the-butcher/MOTH.CO2.2/images/sensor03_800.jpg

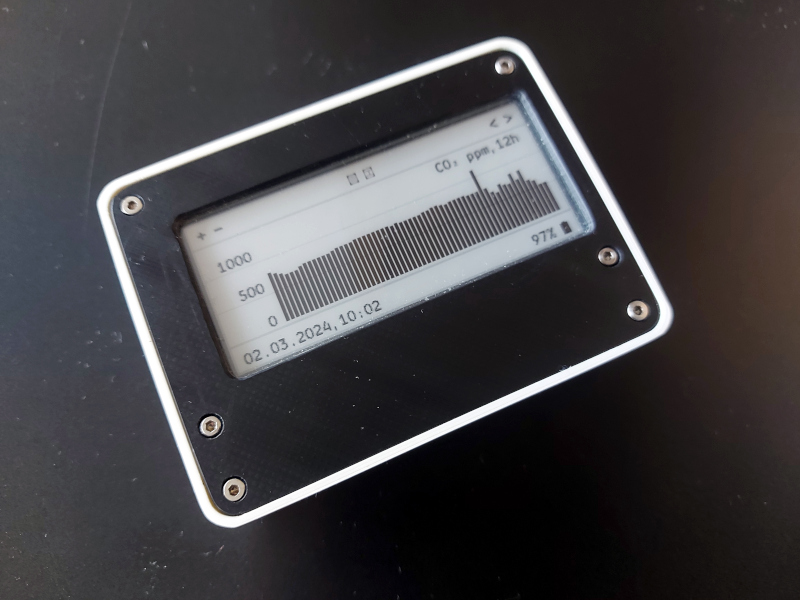
images/sensor03_800.jpg
