the-butcher/MOTH.CO2.2/images/sensor04_800.jpg

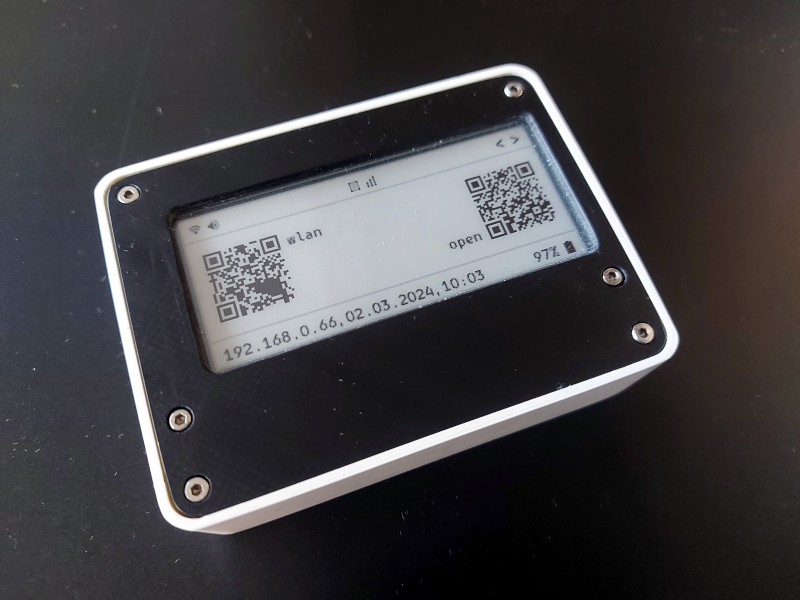
images/sensor04_800.jpg
