the-butcher/MOTH.CO2.2/moth_core/moth_core_022/src/sensors/SensorBme280.h

#ifndef SensorBme280_h
#define SensorBme280_h

#include <Adafruit_Sensor.h>
#include <Arduino.h>
#include <SPI.h>
#include <Wire.h>

#include "SensorBme280Base.h"
#include "types/Config.h"
#include "types/Values.h"

const float ALTITUDE__EXP = 0.190284;
const float ALTITUDE_MULT = 44307.69396;
const float PRESSURE_ZERO = 1013.25;

class SensorBme280 {
   private:
    static SensorBme280Base baseSensor;
    static values_bme_t values;

   public:
    static void begin();
    static bool measure();
    static values_bme_t readval();
    static float getPressureZerolevel(float altitudeBaselevel, float pressure);
    static float getAltitude(float pressureZerolevel, float pressure);
};

#endif
