the-butcher/MOTH.CO2.2/moth_core/moth_core_021/src/SensorScd041Base.h

#ifndef SensorScd041Base_h
#define SensorScd041Base_h

#include <SensirionI2CScd4x.h>

/**
 * subclass of SensirionI2CScd4x implementing a "no delay" version of
 * measureSingleShot
 */
class SensorScd041Base : public SensirionI2CScd4x {
   private:
    TwoWire* _i2cBus = nullptr;

   public:
    void begin(TwoWire& i2cBus);
    uint16_t measureSingleShotNoDelay(void);
};

#endif
