the-butcher/MOTH.CO2.2/moth_core/moth_core_022/src/modules/ModuleDisp.cpp

#include "ModuleDisp.h"

#include <ArduinoJson.h>
#include <qrcode.h>

#include "buttons/ButtonAction.h"
#include "modules/ModuleCard.h"
#include "sensors/SensorBme280.h"
#include "sensors/SensorEnergy.h"
#include "sensors/SensorScd041.h"
#include "sensors/SensorTime.h"
#include "types/Define.h"

const uint16_t LIMIT_POS_X = 287;
const uint8_t CHAR_DIM_X6 = 7;

const rectangle_t RECT_TOP = {1, 1, 295, 22};
const rectangle_t RECT_BOT = {1, 106, 295, 127};
const rectangle_t RECT_CO2 = {1, 22, 207, 106};
const rectangle_t RECT_DEG = {207, 22, 295, 64};
const rectangle_t RECT_HUM = {207, 64, 295, 106};
const rectangle_t RECT_NRG = {279, 112, 288, 125};
const int TEXT_OFFSET_Y = 16;

const char FORMAT_3_DIGIT[] = "%3s";
const char FORMAT_4_DIGIT[] = "%4s";
const char FORMAT_5_DIGIT[] = "%5s";
const char FORMAT_6_DIGIT[] = "%6s";
const char FORMAT_CELL_PERCENT[] = "%5s%%";
const char FORMAT_STALE[] = "%3s%% stale";

ModuleDispBase ModuleDisp::baseDisplay;
bool ModuleDisp::interrupted = false;

void ModuleDisp::configure(config_t& config) {

    ModuleCard::begin();

    File32 dispFileJson;
    bool dispSuccess = dispFileJson.open(DISP_CONFIG_JSON.c_str(), O_RDONLY);
    if (dispSuccess) {
        JsonDocument jsonDocument;
        DeserializationError error = deserializeJson(jsonDocument, dispFileJson);
        if (!error) {

            config.disp.configStatus = CONFIG_STAT__APPLIED;

            // display minutes
            config.disp.displayUpdateMinutes = jsonDocument[JSON_KEY___MINUTES] | config.disp.displayUpdateMinutes;  // apply network expiry (independant from networks)

            // show significant scale
            bool isShowSignificant = jsonDocument[JSON_KEY_______SSC] | config.disp.displayValCycle == DISPLAY_VAL_Y____SIG;
            config.disp.displayValCycle = isShowSignificant ? DISPLAY_VAL_Y____SIG : DISPLAY_VAL_Y____FIX;

            // display co2 threshold and reference
            config.disp.thresholdsCo2.wHi = jsonDocument[JSON_KEY_______CO2][JSON_KEY_WARN_HIGH] | config.disp.thresholdsCo2.wHi;
            config.disp.thresholdsCo2.rHi = jsonDocument[JSON_KEY_______CO2][JSON_KEY_RISK_HIGH] | config.disp.thresholdsCo2.rHi;
            config.disp.thresholdsCo2.ref = jsonDocument[JSON_KEY_______CO2][JSON_KEY_REFERENCE] | config.disp.thresholdsCo2.ref;

            // display deg thresholds
            config.disp.thresholdsDeg.rLo = jsonDocument[JSON_KEY_______DEG][JSON_KEY_RISK__LOW] | config.disp.thresholdsDeg.rLo;
            config.disp.thresholdsDeg.wLo = jsonDocument[JSON_KEY_______DEG][JSON_KEY_WARN__LOW] | config.disp.thresholdsDeg.wLo;
            config.disp.thresholdsDeg.wHi = jsonDocument[JSON_KEY_______DEG][JSON_KEY_WARN_HIGH] | config.disp.thresholdsDeg.wHi;
            config.disp.thresholdsDeg.rHi = jsonDocument[JSON_KEY_______DEG][JSON_KEY_RISK_HIGH] | config.disp.thresholdsDeg.rHi;

            // display deg scale (unit)
            bool isFahrenheit = jsonDocument[JSON_KEY_______DEG][JSON_KEY_______C2F] | config.disp.displayDegScale == DISPLAY_VAL_D______F;
            config.disp.displayDegScale = isFahrenheit ? DISPLAY_VAL_D______F : DISPLAY_VAL_D______C;

            // display deg offset
            config.sco2.temperatureOffset = jsonDocument[JSON_KEY_______DEG][JSON_KEY____OFFSET] | config.sco2.temperatureOffset;
            config.sco2.lpFilterRatioCurr = jsonDocument[JSON_KEY_______CO2][JSON_KEY_______LPA] | config.sco2.lpFilterRatioCurr;
            config.sco2.calibrationCo2Ref = jsonDocument[JSON_KEY_______CO2][JSON_KEY_______CAL] | config.sco2.calibrationCo2Ref;

            // display hum thresholds
            config.disp.thresholdsHum.rLo = jsonDocument[JSON_KEY_______HUM][JSON_KEY_RISK__LOW] | config.disp.thresholdsHum.rLo;
            config.disp.thresholdsHum.wLo = jsonDocument[JSON_KEY_______HUM][JSON_KEY_WARN__LOW] | config.disp.thresholdsHum.wLo;
            config.disp.thresholdsHum.wHi = jsonDocument[JSON_KEY_______HUM][JSON_KEY_WARN_HIGH] | config.disp.thresholdsHum.wHi;
            config.disp.thresholdsHum.rHi = jsonDocument[JSON_KEY_______HUM][JSON_KEY_RISK_HIGH] | config.disp.thresholdsHum.rHi;

            // altitude base level (home altitude of sensor)
            config.sbme.altitudeBaselevel = jsonDocument[JSON_KEY_______BME][JSON_KEY__ALTITUDE] | config.sbme.altitudeBaselevel;
            config.sbme.lpFilterRatioCurr = jsonDocument[JSON_KEY_______BME][JSON_KEY_______LPA] | config.sbme.lpFilterRatioCurr;

            String timezone = jsonDocument[JSON_KEY__TIMEZONE] | "";
            if (timezone != "") {
                timezone.toCharArray(config.time.timezone, 64);
            }

        } else {
            // TODO :: handle this condition
        }
        dispFileJson.close();
    }
}

void ModuleDisp::begin() {
    // do nothing
}

void ModuleDisp::prepareSleep(wakeup_action_e wakeupType) {
    if (wakeupType == WAKEUP_ACTION_BUSY) {
        esp_sleep_enable_ext0_wakeup((gpio_num_t)PIN_EPD_BUSY, HIGH);
    }
}

void ModuleDisp::attachWakeup(wakeup_action_e wakeupType) {
    if (wakeupType == WAKEUP_ACTION_BUSY) {
        attachInterrupt(digitalPinToInterrupt(PIN_EPD_BUSY), ModuleDisp::handleInterrupt, FALLING);
        ModuleDisp::interrupted = false;
    }
}

void ModuleDisp::detachWakeup(wakeup_action_e wakeupType) {
    if (wakeupType == WAKEUP_ACTION_BUSY) {
        detachInterrupt(digitalPinToInterrupt(PIN_EPD_BUSY));
        ModuleDisp::interrupted = false;
    }
}

void ModuleDisp::handleInterrupt() {
    ModuleDisp::interrupted = true;
}

bool ModuleDisp::isInterrupted() {
    return ModuleDisp::interrupted;
}

void ModuleDisp::flushBuffer() {
    ModuleDisp::baseDisplay.writeFrameBuffers();
}

void ModuleDisp::depower() {
    ModuleDisp::baseDisplay.begin(THINKINK_GRAYSCALE4, true);
    ModuleDisp::baseDisplay.depower();
}

void ModuleDisp::clearBuffer(config_t& config) {
    ModuleDisp::baseDisplay.begin(THINKINK_GRAYSCALE4, config.disp.displayValTheme == DISPLAY_THM____LIGHT);
    ModuleDisp::baseDisplay.clearBuffer();
}

void ModuleDisp::renderTable(values_all_t& measurement, config_t& config) {

    ModuleDisp::clearBuffer(config);
    ModuleDisp::drawOuterBorders(EPD_LIGHT);
    ModuleDisp::drawInnerBorders(EPD_LIGHT);

    // values for temperature and humidity
    float deg = SensorScd041::toFloatDeg(measurement.valuesCo2.deg);
    float hum = SensorScd041::toFloatHum(measurement.valuesCo2.hum);

    // variables needed
    String title;
    uint8_t textColor;
    uint8_t fillColor;
    uint8_t vertColor;
    uint16_t xPosMainValue = 36;
    uint16_t charPosValueX = 193;
    uint16_t charPosFinalX;

    if (config.disp.displayValTable == DISPLAY_VAL_T____CO2) {

        thresholds_co2_t thresholdsCo2 = config.disp.thresholdsCo2;
        float co2Lpf = measurement.valuesCo2.co2Lpf / VALUE_SCALE_CO2LPF;

        float stale = max(0.0f, min(10.0f, (co2Lpf - thresholdsCo2.ref) / 380.0f));  // don't allow negative stale values. max out at 10
        float staleWarn = max(0.0f, min(10.0f, (thresholdsCo2.wHi - thresholdsCo2.ref) / 380.0f));
        float staleRisk = max(0.0f, min(10.0f, (thresholdsCo2.rHi - thresholdsCo2.ref) / 380.0f));

        float staleMax = 2.5;
        if (stale > 4) {
            staleMax = 10;
        } else if (stale > 2) {
            staleMax = 5;
        }
        int staleDif = 70 / staleMax;  // height of 1 percent, 20 for staleMax 2.5, 10 for staleMax 5, 5 for staleMax 10

        textColor = getTextColor(co2Lpf, 0, 0, thresholdsCo2.wHi, thresholdsCo2.rHi);
        fillColor = getFillColor(co2Lpf, 0, 0, thresholdsCo2.wHi, thresholdsCo2.rHi);
        vertColor = getVertColor(co2Lpf, 0, 0, thresholdsCo2.wHi, thresholdsCo2.rHi);

        if (fillColor != EPD_WHITE) {
            ModuleDisp::fillRectangle(RECT_CO2, fillColor);
        }

        title = "CO² ppm";
        charPosFinalX = charPosValueX - CHAR_DIM_X6 * 7;
        ModuleDisp::drawAntialiasedText36(formatString(String(co2Lpf, 0), FORMAT_4_DIGIT), RECT_CO2, xPosMainValue, 76, textColor);

        uint8_t yMax = RECT_CO2.ymax - 7;  // bottom limit of rebreathe indicator
        uint8_t yDim = round(stale * staleDif);
        uint8_t yDimWarn = round(staleWarn * staleDif);
        uint8_t yDimRisk = round(staleRisk * staleDif);
        int yDimMax = round(staleMax * staleDif);

        uint8_t xBarMin = 8;
        uint8_t xBarMax = 13;
        for (uint8_t i = xBarMin; i <= xBarMax; i++) {
            ModuleDisp::baseDisplay.drawFastVLine(i, yMax - yDimWarn, yDimWarn, EPD_WHITE);             // good
            ModuleDisp::baseDisplay.drawFastVLine(i, yMax - yDimRisk, yDimRisk - yDimWarn, vertColor);  // warn
            ModuleDisp::baseDisplay.drawFastVLine(i, yMax - yDimMax, yDimMax - yDimRisk, EPD_BLACK);    // risk
        }

        if (ModuleDisp::isRisk(co2Lpf, 0, 0, thresholdsCo2.wHi, thresholdsCo2.rHi)) {  // when in risk, the risk area needs to be outlined
            ModuleDisp::baseDisplay.drawFastVLine(xBarMin, yMax - yDimMax, yDimMax - yDimRisk, vertColor);
            ModuleDisp::baseDisplay.drawFastVLine(xBarMax, yMax - yDimMax, yDimMax - yDimRisk, vertColor);
            ModuleDisp::baseDisplay.drawFastHLine(xBarMin, yMax - yDimMax, xBarMax - xBarMin + 1, vertColor);
        } else if (!ModuleDisp::isWarn(co2Lpf, 0, 0, thresholdsCo2.wHi, thresholdsCo2.rHi)) {  // when not warn and not risk, the good area needs to be outlined
            ModuleDisp::baseDisplay.drawFastVLine(xBarMin, yMax - yDimWarn, yDimWarn, vertColor);
            ModuleDisp::baseDisplay.drawFastVLine(xBarMax, yMax - yDimWarn, yDimWarn, vertColor);
            ModuleDisp::baseDisplay.drawFastHLine(xBarMin, yMax, xBarMax - xBarMin + 1, vertColor);
        }

        uint8_t yTxt = RECT_CO2.ymax - RECT_CO2.ymin - yDim - 10;
        uint8_t yPrc = yTxt;
        uint8_t xPrc = xBarMax + 19;
        uint8_t xLin = 24;

        uint8_t stale10 = round(stale * 10.0);
        uint8_t staleFix = floor(stale10 / 10.0);
        uint8_t staleFrc = abs(stale10 % 10);

        if (stale > 8.5) {
            yTxt += 14;
            yPrc += 14;
        } else if (co2Lpf >= 1000) {  // wrap percent, shorten line
            yPrc += 14;
            xPrc = xBarMax + 2;
            xLin -= CHAR_DIM_X6;
        }

        // draw a narrowed percentage number
        ModuleDisp::baseDisplay.drawFastHLine(xBarMax + 3, yMax - yDim, xLin, textColor);
        ModuleDisp::drawAntialiasedText06(String(staleFix), RECT_CO2, xBarMax + 2, yTxt, textColor);
        if (stale < 10) {
            ModuleDisp::drawAntialiasedText06(".", RECT_CO2, xBarMax + 7, yTxt, textColor);
            ModuleDisp::drawAntialiasedText06(String(staleFrc), RECT_CO2, xBarMax + 12, yTxt, textColor);
        }
        ModuleDisp::drawAntialiasedText06("%", RECT_CO2, xPrc, yPrc, textColor);

    } else if (config.disp.displayValTable == DISPLAY_VAL_T____HPA) {
        float pressure = measurement.valuesBme.pressure;
        textColor = EPD_BLACK;
        fillColor = EPD_WHITE;
        vertColor = EPD_DARK;
        ModuleDisp::fillRectangle(RECT_CO2, fillColor);
        title = "pressure hPa";
        charPosFinalX = charPosValueX - CHAR_DIM_X6 * title.length();
        ModuleDisp::drawAntialiasedText36(formatString(String(pressure, 0), FORMAT_4_DIGIT), RECT_CO2, xPosMainValue, 76, textColor);
    } else if (config.disp.displayValTable == DISPLAY_VAL_T____ALT) {
        float altitude = SensorBme280::getAltitude(config.sbme.pressureZerolevel, measurement.valuesBme.pressure);
        textColor = EPD_BLACK;
        fillColor = EPD_WHITE;
        vertColor = EPD_DARK;
        ModuleDisp::fillRectangle(RECT_CO2, fillColor);
        title = "altitude m";
        charPosFinalX = charPosValueX - CHAR_DIM_X6 * title.length();
        ModuleDisp::drawAntialiasedText36(formatString(String(altitude, 0), FORMAT_4_DIGIT), RECT_CO2, xPosMainValue, 76, textColor);
    } else {
        // TODO :: handle this (unknown display value)
    }
    ModuleDisp::drawAntialiasedText06(title, RECT_CO2, charPosFinalX, TEXT_OFFSET_Y, textColor);

    thresholds_deg_t thresholdsDeg = config.disp.thresholdsDeg;
    textColor = getTextColor(deg, thresholdsDeg.rLo, thresholdsDeg.wLo, thresholdsDeg.wHi, thresholdsDeg.rHi);
    fillColor = getFillColor(deg, thresholdsDeg.rLo, thresholdsDeg.wLo, thresholdsDeg.wHi, thresholdsDeg.rHi);
    if (config.disp.displayDegScale == DISPLAY_VAL_D______F) {
        deg = SensorScd041::toFahrenheit(deg);
    }
    int temperature10 = round(deg * 10.0);
    int temperatureFix = floor(temperature10 / 10.0);
    int temperatureFrc = abs(temperature10 % 10);
    if (fillColor != EPD_WHITE) {
        ModuleDisp::fillRectangle(RECT_DEG, fillColor);
    }
    ModuleDisp::drawAntialiasedText18(formatString(String(temperatureFix), FORMAT_3_DIGIT), RECT_DEG, 0, 35, textColor);
    ModuleDisp::drawAntialiasedText06(config.disp.displayDegScale == DISPLAY_VAL_D______F ? "°F" : "°C", RECT_DEG, 80 - CHAR_DIM_X6 * 2, TEXT_OFFSET_Y + 2, textColor);
    ModuleDisp::drawAntialiasedText08(".", RECT_DEG, 63, 35, textColor);
    ModuleDisp::drawAntialiasedText08(String(temperatureFrc), RECT_DEG, 72, 35, textColor);

    // TODO :: remove after the reason for wifi can not be turned was found and the problem was fixed
    // ModuleDisp::drawAntialiasedText06(String(config.wifi.wifiValPower), RECT_DEG, 7, TEXT_OFFSET_Y + 2, textColor);

    thresholds_hum_t thresholdsHum = config.disp.thresholdsHum;
    textColor = getTextColor(hum, thresholdsHum.rLo, thresholdsHum.wLo, thresholdsHum.wHi, thresholdsHum.rHi);
    fillColor = getFillColor(hum, thresholdsHum.rLo, thresholdsHum.wLo, thresholdsHum.wHi, thresholdsHum.rHi);
    int humidity10 = round(hum * 10.0);
    int humidityFix = floor(humidity10 / 10.0);
    int humidityFrc = abs(humidity10 % 10);
    if (fillColor != EPD_WHITE) {
        ModuleDisp::fillRectangle(RECT_HUM, fillColor);
    }
    ModuleDisp::drawAntialiasedText18(formatString(String(humidityFix), FORMAT_3_DIGIT), RECT_HUM, 0, 35, textColor);
    ModuleDisp::drawAntialiasedText06("%", RECT_HUM, 80 - CHAR_DIM_X6 * 1, TEXT_OFFSET_Y + 2, textColor);
    ModuleDisp::drawAntialiasedText08(".", RECT_HUM, 63, 35, textColor);
    ModuleDisp::drawAntialiasedText08(String(humidityFrc), RECT_HUM, 72, 35, textColor);

    ModuleDisp::renderHeader();
    ModuleDisp::renderFooter(config);

    ModuleDisp::flushBuffer();
}

/**
 * measurement is reference for building the measurement table backwards
 */
void ModuleDisp::renderChart(values_all_t history[60], config_t& config) {

    ModuleDisp::clearBuffer(config);
    ModuleDisp::drawOuterBorders(EPD_LIGHT);

    display_val_c_e displayValChart = config.disp.displayValChart;

    values_all_t measurement;
    uint16_t minValue = 0;
    uint16_t maxValue = 1500;
    if (displayValChart == DISPLAY_VAL_C____CO2) {
        float co2Lpf;
        for (uint8_t i = 0; i < HISTORY_____BUFFER_SIZE; i++) {
            measurement = history[i];
            co2Lpf = measurement.valuesCo2.co2Lpf / VALUE_SCALE_CO2LPF;
            if (co2Lpf > 3600) {
                maxValue = 6000;  // 0, 2000, 4000, (6000)
            } else if (co2Lpf > 2400) {
                maxValue = 4500;  // 0, 1500, 3000, (4500)
            } else if (co2Lpf > 1200) {
                maxValue = 3000;  // 0, 1000, 2000, (3000)
            }
        }
    } else if (displayValChart == DISPLAY_VAL_C____DEG) {
        if (config.disp.displayDegScale == DISPLAY_VAL_D______F) {
            minValue = 60;
            maxValue = 120;
        } else {
            minValue = 10;
            maxValue = 40;
        }
    } else if (displayValChart == DISPLAY_VAL_C____HUM) {
        minValue = 20;
        maxValue = 80;  // 20, 40, 60, (80)
    } else if (displayValChart == DISPLAY_VAL_C____HPA) {
        double pressureAvg = 0;
        uint8_t validValueCount = 0;
        for (uint8_t i = 0; i < HISTORY_____BUFFER_SIZE; i++) {
            measurement = history[i];
            if (measurement.valuesBme.pressure > 0) {
                pressureAvg += measurement.valuesBme.pressure;
                validValueCount++;
            }
        }
        pressureAvg /= validValueCount;                  // lets say it is 998
        minValue = floor(pressureAvg / 10.0) * 10 - 10;  // 99.8 -> 99 -> 990 -> 980
        maxValue = ceil(pressureAvg / 10.0) * 10 + 10;   // 99.8 -> 100 -> 1000 -> 1010
    } else if (displayValChart == DISPLAY_VAL_C____ALT) {
        maxValue = 450;
        float altitude;
        for (uint8_t i = 0; i < HISTORY_____BUFFER_SIZE; i++) {
            measurement = history[i];
            if (measurement.valuesBme.pressure > 0) {
                altitude = SensorBme280::getAltitude(config.sbme.pressureZerolevel, measurement.valuesBme.pressure);
            } else {
                altitude = 0.0f;
            }
            if (altitude > 1600) {
                maxValue = 3600;  // 0, 1200, 2400, 3600
            } else if (altitude > 800) {
                maxValue = 1800;  // 0, 600, 1200, (1800)
            } else if (altitude > 400) {
                maxValue = 900;  // 0, 300, 600, (900)
            }
        }
    } else if (displayValChart == DISPLAY_VAL_C____NRG) {
        double batteryAvg = 0;
        float batteryVal;
        float batteryMin = 100;
        float batteryMax = 0;
        uint8_t validValueCount = 0;
        for (uint8_t i = 0; i < HISTORY_____BUFFER_SIZE; i++) {
            measurement = history[i];
            if (measurement.valuesBme.pressure > 0) {  // is it a valid value?
                batteryVal = SensorEnergy::toFloatPercent(measurement.valuesNrg.percent);
                batteryMin = min(batteryMin, batteryVal);
                batteryMax = max(batteryMax, batteryVal);
                batteryAvg += batteryVal;
                validValueCount++;
            }
        }
        batteryAvg /= validValueCount;
        batteryAvg = round(batteryAvg);

        double batteryDif = max(2.0, ceil((batteryMax - batteryMin) / 2.0));  // half dif from min to max, min 1
        if (batteryAvg > 50) {
            maxValue = min(100.0, batteryAvg + batteryDif);  // avg + dif (but not more than 100)
            minValue = maxValue - batteryDif * 2;
        } else {
            minValue = max(0.0, batteryAvg - batteryDif);  // avg - dif (but not less than zero)
            maxValue = minValue + batteryDif * 2;
        }
        maxValue += batteryDif;  // room for text
    }

    String label2 = String(minValue + (maxValue - minValue) * 2 / 3);
    String label1 = String(minValue + (maxValue - minValue) / 3);
    String label0 = String(minValue);

    uint8_t charPosValueX = 41;
    uint8_t charPosLabelY = 12;

    ModuleDisp::drawAntialiasedText06(label2, RECT_CO2, charPosValueX - CHAR_DIM_X6 * label2.length(), 24, EPD_BLACK);
    ModuleDisp::baseDisplay.drawFastHLine(1, 49, 296, EPD_LIGHT);
    ModuleDisp::drawAntialiasedText06(label1, RECT_CO2, charPosValueX - CHAR_DIM_X6 * label1.length(), 52, EPD_BLACK);
    ModuleDisp::baseDisplay.drawFastHLine(1, 77, 296, EPD_LIGHT);
    ModuleDisp::drawAntialiasedText06(label0, RECT_CO2, charPosValueX - CHAR_DIM_X6 * label0.length(), 80, EPD_BLACK);

    values_all_t lastMeasurement = history[HISTORY_____BUFFER_SIZE - 1];
    String label;
    String value;
    String vunit;
    if (displayValChart == DISPLAY_VAL_C____CO2) {
        label = "CO²";
        value = String(lastMeasurement.valuesCo2.co2Lpf / VALUE_SCALE_CO2LPF, 0);
        vunit = "ppm";
    } else if (displayValChart == DISPLAY_VAL_C____DEG) {
        label = "temperature";
        value = String(SensorScd041::toFloatDeg(lastMeasurement.valuesCo2.deg), 1);
        vunit = config.disp.displayDegScale == DISPLAY_VAL_D______F ? "°F" : "°C";
    } else if (displayValChart == DISPLAY_VAL_C____HUM) {
        label = "humidity";
        value = String(SensorScd041::toFloatHum(lastMeasurement.valuesCo2.hum), 1);
        vunit = "%";
    } else if (displayValChart == DISPLAY_VAL_C____HPA) {
        label = "pressure";
        value = String(lastMeasurement.valuesBme.pressure, 0);
        vunit = "hPa";
    } else if (displayValChart == DISPLAY_VAL_C____ALT) {
        label = "altitude";
        if (measurement.valuesBme.pressure > 0) {
            value = String(SensorBme280::getAltitude(config.sbme.pressureZerolevel, lastMeasurement.valuesBme.pressure), 0);
        } else {
            value = String(0.0f, 0);
        }
        vunit = "m";  // TODO :: allow feet (?)
    } else if (displayValChart == DISPLAY_VAL_C____NRG) {
        label = "battery";
        value = String(SensorEnergy::toFloatPercent(lastMeasurement.valuesNrg.percent), 0);
        vunit = "%";
    }

    char titleBuffer[32];
    sprintf(titleBuffer, "%s (%s%s),%dh", label, value, vunit, config.disp.displayHrsChart);
    String title = String(titleBuffer);

    ModuleDisp::drawAntialiasedText06(title, RECT_CO2, LIMIT_POS_X - title.length() * CHAR_DIM_X6 + 1, charPosLabelY, EPD_BLACK);

    uint16_t minX;
    uint8_t minY;
    uint8_t maxY = 103;
    uint8_t dimY;
    uint8_t limY = 78.0;
    float curValue;

    uint8_t displayableBarWidth = 240 / HISTORY_____BUFFER_SIZE;
    uint8_t basX = LIMIT_POS_X - HISTORY_____BUFFER_SIZE * displayableBarWidth;
    for (uint8_t i = 0; i < HISTORY_____BUFFER_SIZE; i++) {

        measurement = history[i];

        if (displayValChart == DISPLAY_VAL_C____CO2) {
            curValue = measurement.valuesCo2.co2Lpf / VALUE_SCALE_CO2LPF;
        } else if (displayValChart == DISPLAY_VAL_C____DEG) {
            curValue = SensorScd041::toFloatDeg(measurement.valuesCo2.deg);
            if (config.disp.displayDegScale == DISPLAY_VAL_D______F) {
                curValue = SensorScd041::toFahrenheit(curValue);
            }
        } else if (displayValChart == DISPLAY_VAL_C____HUM) {
            curValue = SensorScd041::toFloatHum(measurement.valuesCo2.hum);
        } else if (displayValChart == DISPLAY_VAL_C____HPA) {
            curValue = measurement.valuesBme.pressure;
        } else if (displayValChart == DISPLAY_VAL_C____ALT) {
            if (measurement.valuesBme.pressure > 0) {
                curValue = SensorBme280::getAltitude(config.sbme.pressureZerolevel, measurement.valuesBme.pressure);
            } else {
                curValue = 0.0f;
            }
        } else if (displayValChart == DISPLAY_VAL_C____NRG) {
            curValue = SensorEnergy::toFloatPercent(measurement.valuesNrg.percent);
        }

        minX = basX + i * displayableBarWidth;
        dimY = max(0, min((int)limY, (int)round((curValue - minValue) * limY / (maxValue - minValue))));
        minY = maxY - dimY;

        if (dimY > 0) {
            for (int b = 0; b < displayableBarWidth - 1; b++) {
                baseDisplay.drawFastVLine(minX + b, minY, dimY, EPD_BLACK);
            }
        } else {
            // indicator lines
            // baseDisplay.drawFastHLine(minX, minY - 1, displayableBarWidth - 1, EPD_BLACK);
        }
    }

    ModuleDisp::renderHeader();
    ModuleDisp::renderFooter(config);

    ModuleDisp::flushBuffer();
}

void ModuleDisp::renderCo2Cal(co2cal______t co2cal, config_t& config) {

    ModuleDisp::clearBuffer(config);
    ModuleDisp::drawOuterBorders(EPD_LIGHT);

    values_all_t measurement;
    uint16_t minValue = co2cal.minValue - 50;
    uint16_t maxValue = co2cal.maxValue + 50;

    uint16_t minX;
    uint8_t minY;
    uint8_t maxY = 103;
    uint8_t dimY;
    uint8_t limY = 78;
    float curValue;

    curValue = co2cal.avgValue - co2cal.devValue;
    dimY = max(0, min((int)limY, (int)round((curValue - minValue) * limY / (maxValue - minValue))));
    uint8_t maxD = max((uint8_t)22, min((uint8_t)105, (uint8_t)(maxY - dimY)));
    curValue = co2cal.avgValue + co2cal.devValue;
    dimY = max(0, min((int)limY, (int)round((curValue - minValue) * limY / (maxValue - minValue))));
    uint8_t minD = max((uint8_t)22, min((uint8_t)105, (uint8_t)(maxY - dimY)));

    for (uint8_t devD = minD; devD <= maxD; devD++) {
        baseDisplay.drawFastHLine(5, devD, 286, EPD_LIGHT);
    }

    uint8_t displayableBarWidth = 220 / CALIBRATION_BUFFER_SIZE;
    uint8_t basX = LIMIT_POS_X - CALIBRATION_BUFFER_SIZE * displayableBarWidth;
    for (uint8_t i = 0; i < CALIBRATION_BUFFER_SIZE; i++) {

        curValue = co2cal.values[i];

        minX = basX + i * displayableBarWidth;
        dimY = max(0, min((int)limY, (int)round((curValue - minValue) * limY / (maxValue - minValue))));
        minY = maxY - dimY;

        if (dimY > 0) {
            for (int b = 0; b < displayableBarWidth - 1; b++) {
                baseDisplay.drawFastVLine(minX + b, minY, dimY, EPD_DARK);  // draw line top down
            }
        } else {
            // indicator lines
            // baseDisplay.drawFastHLine(minX, minY - 1, displayableBarWidth - 1, EPD_BLACK);
        }
    }

    // avg indicator line
    curValue = co2cal.avgValue;
    dimY = max(0, min((int)limY, (int)round((curValue - minValue) * limY / (maxValue - minValue))));
    minY = maxY - dimY;
    baseDisplay.drawFastHLine(5, minY, 286, EPD_BLACK);

    String labelAvg = String(curValue, 0);
    String labelDev = String(co2cal.devValue);
    String labelTop = String(co2cal.maxValue);
    String labelBot = String(co2cal.minValue);
    if (co2cal.type == CO2CAL_SUCCESS) {
        labelTop = "success";
        labelBot = String(co2cal.corValue);
    } else if (co2cal.type == CO2CAL_FAILURE) {
        labelTop = "failure";
        labelBot = "";
    }

    uint8_t charPosValueX = 61;
    uint8_t charPosValueY = minY - 4;
    ModuleDisp::drawAntialiasedText06(labelAvg, RECT_TOP, charPosValueX - CHAR_DIM_X6 * labelAvg.length(), charPosValueY, EPD_BLACK);       // use RECT_TOP becuase it refers to Y=0
    ModuleDisp::drawAntialiasedText06(labelDev, RECT_TOP, charPosValueX - CHAR_DIM_X6 * labelDev.length(), charPosValueY + 14, EPD_BLACK);  // use RECT_TOP becuase it refers to Y=0
    ModuleDisp::drawAntialiasedText06(labelTop, RECT_CO2, charPosValueX - CHAR_DIM_X6 * labelTop.length(), 12, EPD_BLACK);
    ModuleDisp::drawAntialiasedText06(labelBot, RECT_CO2, charPosValueX - CHAR_DIM_X6 * labelBot.length(), 80, EPD_BLACK);

    ModuleDisp::renderHeader();
    ModuleDisp::renderFooter(config);

    ModuleDisp::flushBuffer();
}

void ModuleDisp::renderHeader() {
    renderButton(ButtonAction::A.buttonAction, 6);
    renderButton(ButtonAction::B.buttonAction, 135);
    renderButton(ButtonAction::C.buttonAction, 264);
}

void ModuleDisp::renderButton(button_action_t buttonAction, uint16_t x) {
    ModuleDisp::drawAntialiasedText08(buttonAction.symbolSlow, RECT_TOP, x, TEXT_OFFSET_Y, EPD_BLACK);
    ModuleDisp::drawAntialiasedText08(buttonAction.symbolFast, RECT_TOP, x + CHAR_DIM_X6 * 2, TEXT_OFFSET_Y, EPD_BLACK);
    ModuleDisp::drawAntialiasedText06(buttonAction.extraLabel, RECT_TOP, x + CHAR_DIM_X6 * 4, TEXT_OFFSET_Y - 2, EPD_BLACK);
}

void ModuleDisp::renderFooter(config_t& config) {

    values_nrg_t valuesEnergy = SensorEnergy::readval();
    float percent = SensorEnergy::toFloatPercent(valuesEnergy.percent);

    String cellPercentFormatted = formatString(String(percent, 0), FORMAT_CELL_PERCENT);
    ModuleDisp::drawAntialiasedText06(cellPercentFormatted, RECT_BOT, LIMIT_POS_X - 14 - CHAR_DIM_X6 * cellPercentFormatted.length(), TEXT_OFFSET_Y, EPD_BLACK);

    // main battery frame
    ModuleDisp::fillRectangle(RECT_NRG, EPD_LIGHT);

    // percentage
    uint8_t yMin = RECT_NRG.ymax - 3 - (uint8_t)round((RECT_NRG.ymax - RECT_NRG.ymin - 3) * percent * 0.01f);
    fillRectangle({RECT_NRG.xmin, yMin, RECT_NRG.xmax, RECT_NRG.ymax}, EPD_BLACK);

    // battery contact clip
    ModuleDisp::baseDisplay.drawFastHLine(RECT_NRG.xmin + 1, RECT_NRG.ymin + 1, 2, EPD_WHITE);
    ModuleDisp::baseDisplay.drawFastHLine(RECT_NRG.xmax - 3, RECT_NRG.ymin + 1, 2, EPD_WHITE);

    int charPosFooter = 7;
    if (config.sign.signalValSound == SIGNAL__VAL______ON) {
        ModuleDisp::drawAntialiasedText08(SYMBOL_YBEEP, RECT_BOT, 6, TEXT_OFFSET_Y + 1, EPD_BLACK);
        charPosFooter += 13;
    }

    if (config.wifi.wifiValPower == WIFI____VAL_P__CUR_Y) {
        String address = ModuleWifi::getAddress();
        ModuleDisp::drawAntialiasedText06(address, RECT_BOT, charPosFooter, TEXT_OFFSET_Y, EPD_BLACK);
        ModuleDisp::drawAntialiasedText06(",", RECT_BOT, charPosFooter + address.length() * CHAR_DIM_X6, TEXT_OFFSET_Y, EPD_BLACK);
        charPosFooter += (address.length() + 1) * CHAR_DIM_X6;
    }
    ModuleDisp::drawAntialiasedText06(SensorTime::getDateTimeDisplayString(SensorTime::getSecondstime()), RECT_BOT, charPosFooter, TEXT_OFFSET_Y, EPD_BLACK);
}

void ModuleDisp::renderEntry(config_t& config) {
    ModuleDisp::clearBuffer(config);
    ModuleDisp::drawOuterBorders(EPD_LIGHT);

    drawAntialiasedText18("moth", RECT_TOP, 8, 98, EPD_BLACK);
    drawAntialiasedText06(VNUM, RECT_TOP, 105, 98, EPD_BLACK);
    drawAntialiasedText06(String(Config::getUtcOffsetSeconds()), RECT_TOP, 180, 98, EPD_BLACK);

    // skip header for clean screen
    ModuleDisp::renderFooter(config);

    ModuleDisp::flushBuffer();
}

void ModuleDisp::renderQRCodes(config_t& config) {
    ModuleDisp::clearBuffer(config);
    ModuleDisp::drawOuterBorders(EPD_LIGHT);

    // either http://ap_ip/login or [PREF_A_WIFI] + IP
    String address = ModuleWifi::getRootUrl();
    String networkName = ModuleWifi::getNetworkName();
    String networkPass = ModuleWifi::getNetworkPass();

    int qrCodeX = 12;
    int qrCodeY = 35;

    // render the network connection link
    if (networkName != "") {
        char networkBuf[networkName.length() + 1];
        networkName.toCharArray(networkBuf, networkName.length() + 1);

        QRCode qrcodeNetwork;
        uint8_t qrcodeDataNetwork[qrcode_getBufferSize(3)];
        qrcode_initText(&qrcodeNetwork, qrcodeDataNetwork, 3, 0, networkBuf);

        for (uint8_t y = 0; y < qrcodeNetwork.size; y++) {
            for (uint8_t x = 0; x < qrcodeNetwork.size; x++) {
                if (qrcode_getModule(&qrcodeNetwork, x, y)) {
                    baseDisplay.fillRect(x * 2 + qrCodeX, y * 2 + qrCodeY, 2, 2, EPD_BLACK);
                }
            }
        }

        qrCodeX = 228;

        ModuleDisp::drawAntialiasedText06("wlan", RECT_TOP, 75, 45, EPD_BLACK);
        if (networkPass != "") {
            ModuleDisp::drawAntialiasedText06(ModuleWifi::getNetworkPass(), RECT_TOP, 75, 60, EPD_BLACK);
        }
        ModuleDisp::drawAntialiasedText06("open", RECT_TOP, 193, 89, EPD_BLACK);
    }

    char addressBuf[address.length() + 1];
    address.toCharArray(addressBuf, address.length() + 1);

    QRCode qrcodeAddress;
    uint8_t qrcodeDataAddress[qrcode_getBufferSize(3)];
    qrcode_initText(&qrcodeAddress, qrcodeDataAddress, 3, 0, addressBuf);

    // render the ip address within the network
    for (uint8_t y = 0; y < qrcodeAddress.size; y++) {
        for (uint8_t x = 0; x < qrcodeAddress.size; x++) {
            if (qrcode_getModule(&qrcodeAddress, x, y)) {
                baseDisplay.fillRect(x * 2 + qrCodeX, y * 2 + qrCodeY, 2, 2, EPD_BLACK);
            }
        }
    }

    ModuleDisp::renderHeader();
    ModuleDisp::renderFooter(config);

    ModuleDisp::flushBuffer();
}

void ModuleDisp::drawAntialiasedText06(String text, rectangle_t rectangle, int xRel, int yRel, uint8_t color) {
    drawAntialiasedText(text, rectangle, xRel, yRel, color, &smb06pt_l, &smb06pt_d, &smb06pt_b);
}

void ModuleDisp::drawAntialiasedText08(String text, rectangle_t rectangle, int xRel, int yRel, uint8_t color) {
    drawAntialiasedText(text, rectangle, xRel, yRel, color, &smb08pt_l, &smb08pt_d, &smb08pt_b);
}

void ModuleDisp::drawAntialiasedText18(String text, rectangle_t rectangle, int xRel, int yRel, uint8_t color) {
    drawAntialiasedText(text, rectangle, xRel, yRel, color, &smb18pt_l, &smb18pt_d, &smb18pt_b);
}

void ModuleDisp::drawAntialiasedText36(String text, rectangle_t rectangle, int xRel, int yRel, uint8_t color) {
    drawAntialiasedText(text, rectangle, xRel, yRel, color, &smb36pt_l, &smb36pt_d, &smb36pt_b);
}

/**
 * when switching fonts, setFont(...) must be called before setCursor(...), or there may be a y-offset on the very first text
 */
void ModuleDisp::drawAntialiasedText(String text, rectangle_t rectangle, int xRel, int yRel, uint8_t color, const GFXfont* fontL, const GFXfont* fontD, const GFXfont* fontB) {
    ModuleDisp::baseDisplay.setFont(fontL);
    ModuleDisp::baseDisplay.setCursor(rectangle.xmin + xRel, rectangle.ymin + yRel);
    ModuleDisp::baseDisplay.setTextColor(color == EPD_BLACK ? EPD_LIGHT : EPD_DARK);
    ModuleDisp::baseDisplay.print(text);

    ModuleDisp::baseDisplay.setFont(fontD);
    ModuleDisp::baseDisplay.setCursor(rectangle.xmin + xRel, rectangle.ymin + yRel);
    ModuleDisp::baseDisplay.setTextColor(color == EPD_BLACK ? EPD_DARK : EPD_LIGHT);
    ModuleDisp::baseDisplay.print(text);

    ModuleDisp::baseDisplay.setFont(fontB);
    ModuleDisp::baseDisplay.setCursor(rectangle.xmin + xRel, rectangle.ymin + yRel);
    ModuleDisp::baseDisplay.setTextColor(color);
    ModuleDisp::baseDisplay.print(text);
}

void ModuleDisp::drawOuterBorders(uint16_t color) {
    // top
    ModuleDisp::baseDisplay.drawFastHLine(0, 0, 296, color);
    ModuleDisp::baseDisplay.drawFastHLine(0, 1, 296, color);
    // footer separator
    ModuleDisp::baseDisplay.drawFastHLine(0, 105, 296, color);
    ModuleDisp::baseDisplay.drawFastHLine(0, 106, 296, color);
    // header separator
    ModuleDisp::baseDisplay.drawFastHLine(0, 21, 296, color);
    ModuleDisp::baseDisplay.drawFastHLine(0, 22, 296, color);
    // bottom
    ModuleDisp::baseDisplay.drawFastHLine(0, 126, 296, color);
    ModuleDisp::baseDisplay.drawFastHLine(0, 127, 296, color);
    // left
    ModuleDisp::baseDisplay.drawFastVLine(0, 0, 128, color);
    ModuleDisp::baseDisplay.drawFastVLine(1, 0, 128, color);
    // right
    ModuleDisp::baseDisplay.drawFastVLine(294, 0, 128, color);
    ModuleDisp::baseDisplay.drawFastVLine(295, 0, 128, color);
}

void ModuleDisp::drawInnerBorders(uint16_t color) {
    // horizontal center
    ModuleDisp::baseDisplay.drawFastHLine(206, 63, 100, color);
    ModuleDisp::baseDisplay.drawFastHLine(206, 64, 100, color);
    // vertical center
    ModuleDisp::baseDisplay.drawFastVLine(206, 21, 86, color);
    ModuleDisp::baseDisplay.drawFastVLine(207, 22, 86, color);
}

void ModuleDisp::fillRectangle(rectangle_t rectangle, uint8_t color) {
    ModuleDisp::baseDisplay.fillRect(rectangle.xmin + 1, rectangle.ymin + 1, rectangle.xmax - rectangle.xmin - 2, rectangle.ymax - rectangle.ymin - 2, color);
}

bool ModuleDisp::isWarn(float value, uint16_t rLo, uint16_t warnLo, uint16_t wHi, uint16_t rHi) {
    return value < warnLo || value >= wHi;
}

bool ModuleDisp::isRisk(float value, uint16_t rLo, uint16_t warnLo, uint16_t wHi, uint16_t rHi) {
    return value < rLo || value >= rHi;
}

uint8_t ModuleDisp::getTextColor(float value, uint16_t rLo, uint16_t warnLo, uint16_t wHi, uint16_t rHi) {
    if (ModuleDisp::isRisk(value, rLo, warnLo, wHi, rHi)) {
        return EPD_WHITE;
    } else {
        return EPD_BLACK;
    }
}

uint8_t ModuleDisp::getFillColor(float value, uint16_t rLo, uint16_t warnLo, uint16_t wHi, uint16_t rHi) {
    if (ModuleDisp::isRisk(value, rLo, warnLo, wHi, rHi)) {
        return EPD_BLACK;
    } else if (ModuleDisp::isWarn(value, rLo, warnLo, wHi, rHi)) {
        return EPD_LIGHT;
    } else {
        return EPD_WHITE;
    }
}

uint8_t ModuleDisp::getVertColor(float value, uint16_t rLo, uint16_t warnLo, uint16_t wHi, uint16_t rHi) {
    if (ModuleDisp::isRisk(value, rLo, warnLo, wHi, rHi)) {
        return EPD_LIGHT;
    } else {
        return EPD_DARK;
    }
}

String ModuleDisp::formatString(String value, char const* format) {
    char padBuffer[16];
    sprintf(padBuffer, format, value);
    return padBuffer;
}
