the-butcher/MOTH.CO2.2/moth_core/moth_core_p01/src/modules/File32Response.h

#ifndef File32Response_h
#define File32Response_h

#include <Arduino.h>
#include <ESPAsyncWebServer.h>
#include <sensors/SensorTime.h>

// from https://github.com/me-no-dev/ESPAsyncWebServer/blob/master/src/WebResponseImpl.h

class File32Response : public AsyncAbstractResponse {
   private:
    File _content;
    String _path;
    String lastModified;

   public:
    File32Response(String path, String contentType);
    ~File32Response();
    bool wasModifiedSince(String ifModifiedSince);
    bool _sourceValid() const {
        return !!(_content);
    }
    virtual size_t _fillBuffer(uint8_t *buf, size_t maxLen) override;
};

#endif
