the-butcher/MOTH.CO2.2/moth_core/moth_core_p01/src/modules/ModuleSignal.h

#ifndef ModuleSignal_h
#define ModuleSignal_h

#include <Arduino.h>
#include <driver/rtc_io.h>

#include "types/Define.h"

typedef enum : uint32_t {
    COLOR____WHITE = 0x333333,
    COLOR______RED = 0xFF0000,
    COLOR___ORANGE = 0x375A00,
    COLOR____GREEN = 0x00FF00,
    COLOR___YELLOW = 0x333300,
    COLOR_____BLUE = 0x0000FF,
    COLOR____OCEAN = 0x000011,
    COLOR_____CYAN = 0x003333,
    COLOR__MAGENTA = 0x660066,
    COLOR____BLACK = 0x000000,
    COLOR_____GRAY = 0x060606
} color_t;

const uint16_t BUZZER____FREQ_LO = 1000;
const uint8_t BUZZER____CHANNEL = 0;
const uint8_t BUZZER_RESOLUTION = 8;  // 0 - 255
const gpio_num_t BUZZER_______GPIO = GPIO_NUM_8;

class ModuleSignal {
   private:
    static color_t pixelColor;

   public:
    static void begin();
    static void beep();
    static void beep(uint16_t frequency);
    static color_t getPixelColor();
    static void setPixelColor(color_t pixelColor);
};

#endif
