the-butcher/MOTH.CO2.2/moth_core/moth_core_p01/src/modules/ValcsvResponse.h

#ifndef ValcsvResponse_h
#define ValcsvResponse_h

#include <Arduino.h>
#include <ESPAsyncWebServer.h>

#include "sensors/SensorTime.h"
#include "types/Values.h"

// from https://github.com/me-no-dev/ESPAsyncWebServer/blob/master/src/WebResponseImpl.h

class ValcsvResponse : public AsyncAbstractResponse {
   private:
    bool firstFill;
    uint8_t lineLimit;

   public:
    ValcsvResponse();
    ~ValcsvResponse();
    bool _sourceValid() const {
        return true;
    }
    virtual size_t _fillBuffer(uint8_t* buf, size_t maxLen) override;
};

#endif
