the-butcher/MOTH.CO2.2/moth_core/moth_core_022/src/buttons/ButtonHelper.cpp

#include "ButtonHelper.h"

ButtonHelper::ButtonHelper(gpio_num_t gpin) {
    this->gpin = gpin;
    this->ipin = digitalPinToInterrupt(gpin);
    this->buttonAction = {"", "", "", nullptr, nullptr};
}

void ButtonHelper::begin() {
    rtc_gpio_deinit(gpin);
    pinMode(gpin, INPUT_PULLUP);
}

void ButtonHelper::prepareSleep(wakeup_action_e wakeupType) {
    if (wakeupType == WAKEUP_ACTION_BUTN) {
        gpio_hold_en(gpin);
        rtc_gpio_pullup_en(gpin);
        rtc_gpio_pulldown_dis(gpin);
    } else {
        gpio_hold_dis(gpin);
    }
}

bool ButtonHelper::isPressed() {
    return digitalRead(gpin) == LOW;
}
