the-butcher/MOTH.CO2.2/moth_core/moth_core_021/src/BoxClock.h

#ifndef BoxClock_h
#define BoxClock_h

#include "RTClib.h"
#include "DataFileDef.h"
#include "BoxDisplay.h"
#include "ButtonHandlers.h"

class BoxClock {
  
  private:
    static RTC_PCF8523 baseClock;
    static int64_t timeUpdateCounter;
    static void handleNtpUpdate(struct timeval *t);

    
  public:
    static void setTimezone(String timezone);
    static String getTimezone();
    static void begin();
    static DateTime getDate();
    static bool isUpdateable();
    static void optNtpUpdate();
    static String getDateTimeDisplayString(DateTime date);
    static String getDateTimeString(DateTime date);
    static DataFileDef getDataFileDef(DateTime date);
    static void disableGpioWakeupSources();
    static void enableGpioWakeupSources();

};

#endif
