the-butcher/MOTH.CO2.2/moth_core/moth_core_021/src/ButtonHandlers.h

#ifndef ButtonHandlers_h
#define ButtonHandlers_h

#include "Arduino.h"
#include "LoopReason.h"
#include "ButtonHandler.h"

class ButtonHandlers {
  
  private:
  
  public:
    static ButtonHandler A;
    static ButtonHandler B;
    static ButtonHandler C;
    static void begin();
    static void assignChartHours();
    static void assignWifiAndPms();
    static void assignAltitudeModifiers();
    static void assignThemeAndState();

};

#endif
