the-butcher/MOTH.CO2.2/moth_core/moth_core_021/src/Measurement.h

#ifndef Measurement_h
#define Measurement_h

#include "ValuesCo2.h"
#include "ValuesBme.h"
#include "ValuesPms.h"
#include "ValuesBat.h"

typedef struct {
  uint32_t secondstime;
  ValuesCo2 valuesCo2; 
  ValuesPms valuesPms;
  ValuesBme valuesBme;
  ValuesBat valuesBat;
  bool publishable;
} Measurement;

#endif
