the-butcher/MOTH.CO2.2/moth_core/moth_core_021/src/ValuesPms.h

#ifndef ValuesPms_h
#define ValuesPms_h

typedef struct {
  float pm010;
  float pm025;
  float pm100;
  int pc003;
  int pc005;
  int pc010;
  int pc025;
  int pc050;
  int pc100;
} ValuesPms;

#endif
