the-butcher/MOTH.CO2.2/moth_core/moth_core_021/src/BoxStatus.h

#ifndef BoxStatus_h
#define BoxStatus_h

typedef enum {
  CONFIG_STATUS_PENDING,
  CONFIG_STATUS_PRESENT,
  CONFIG_STATUS_MISSING,
  CONFIG_STATUS__LOADED,
  CONFIG_STATUS__PARSED
} config_status_t;

#endif
